Xinyuan-LilyGO/T-QT-C6/examples/Lvgl_CIT_ETA4662/widgets_init.h

/*
 * @Description: None
 * @version: V1.0.0
 * @Author: LILYGO_L
 * @Date: 2023-12-08 10:45:26
 * @LastEditors: LILYGO_L
 * @LastEditTime: 2024-06-03 15:22:37
 * @License: GPL 3.0
 */

#ifndef WIDGET_INIT_H
#define WIDGET_INIT_H
#ifdef __cplusplus
extern "C" {
#endif

#include "lvgl.h"
#include "gui_guider.h"

__attribute__((unused)) void kb_event_cb(lv_event_t *e);
__attribute__((unused)) void ta_event_cb(lv_event_t *e);
#if LV_USE_ANALOGCLOCK != 0
void clock_count(int *hour, int *min, int *sec);
#endif



#ifdef __cplusplus
}
#endif
#endif
